hamityanik/ULP-Weather-Logger/Arduino-Example-Code/images/2.png

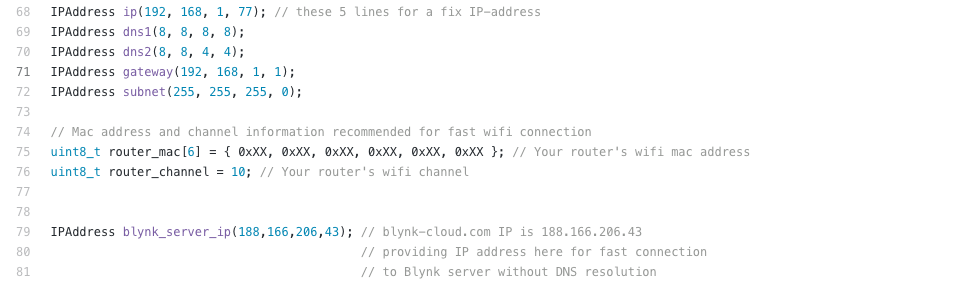
Arduino-Example-Code/images/2.png
