hamityanik/ULP-Weather-Logger/Images/@2.4v.png

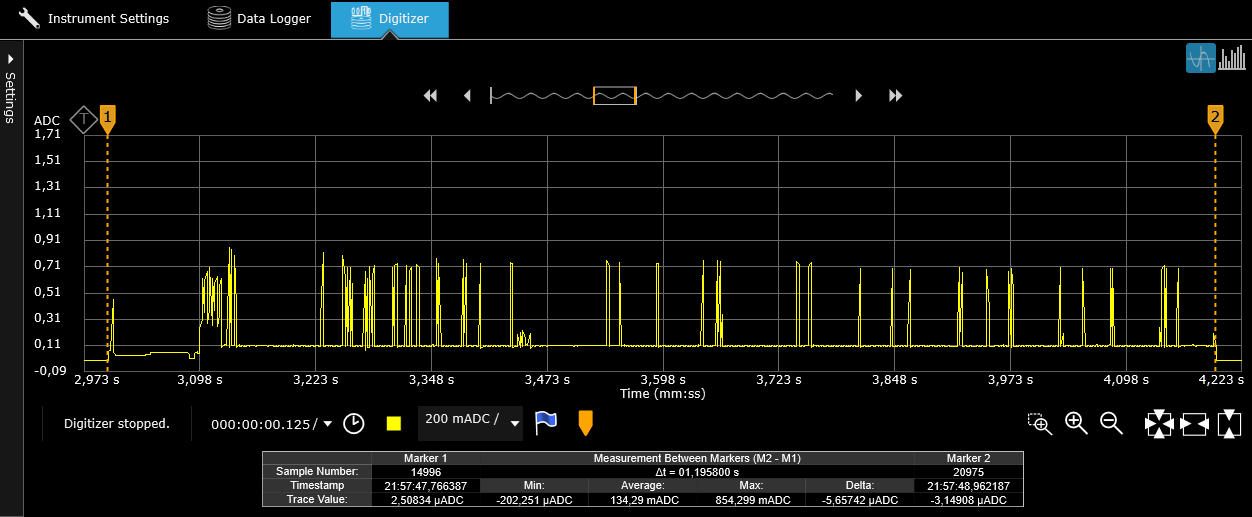
Images/@2.4v.png
