hamityanik/ULP-Weather-Logger/Images/@2v.png

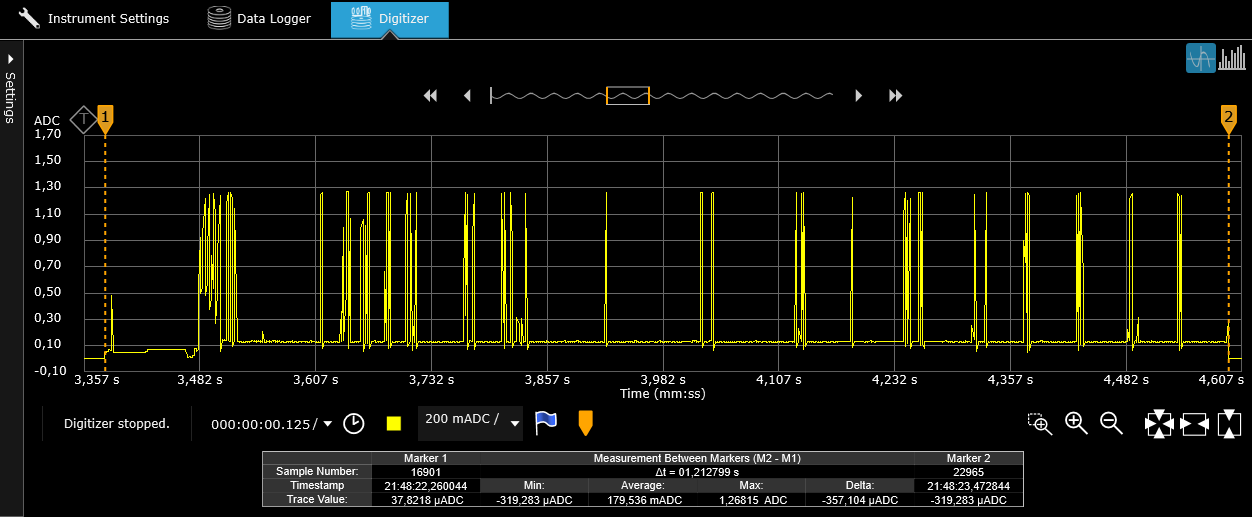
Images/@2v.png
