hamityanik/ULP-Weather-Logger/Images/_20170111_074019.JPG

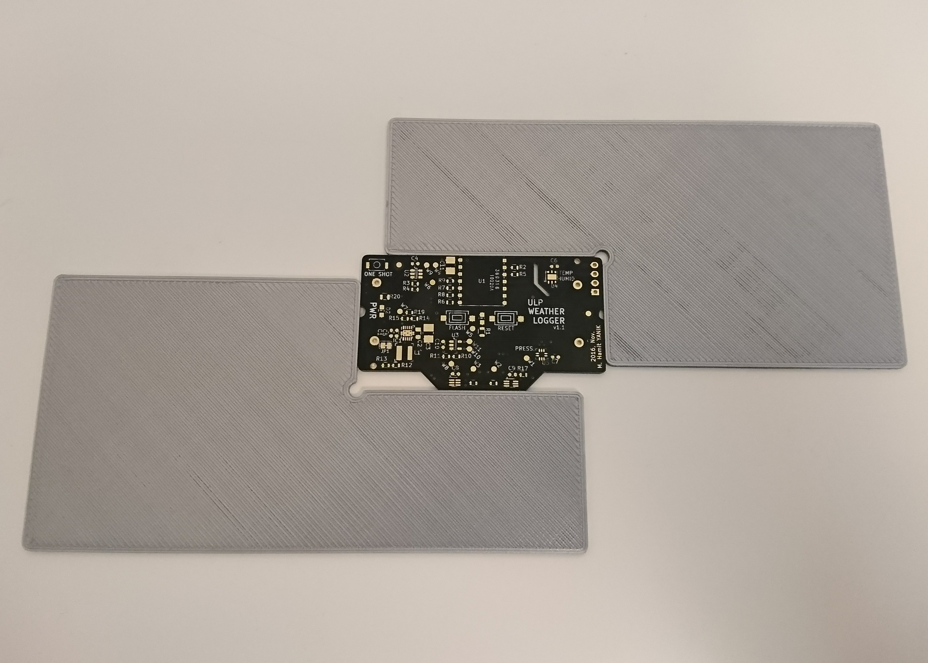
Images/_20170111_074019.JPG
