hamityanik/ULP-Weather-Logger/Images/DSC08371-v1.0.JPG

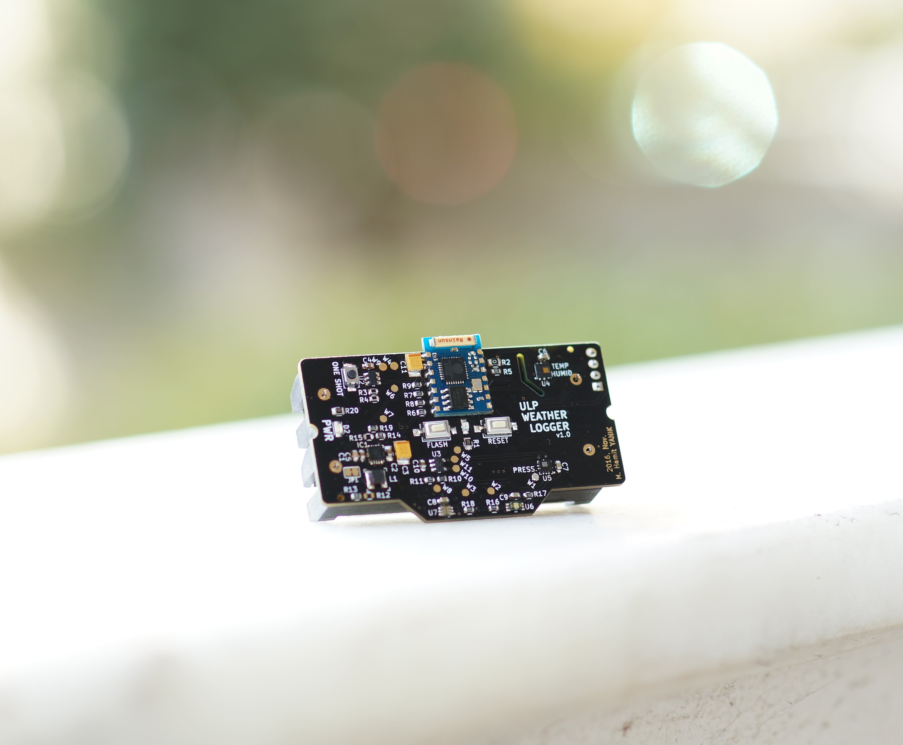
Images/DSC08371-v1.0.JPG
