hamityanik/ULP-Weather-Logger/Images/IMG_-4cxao2.jpg

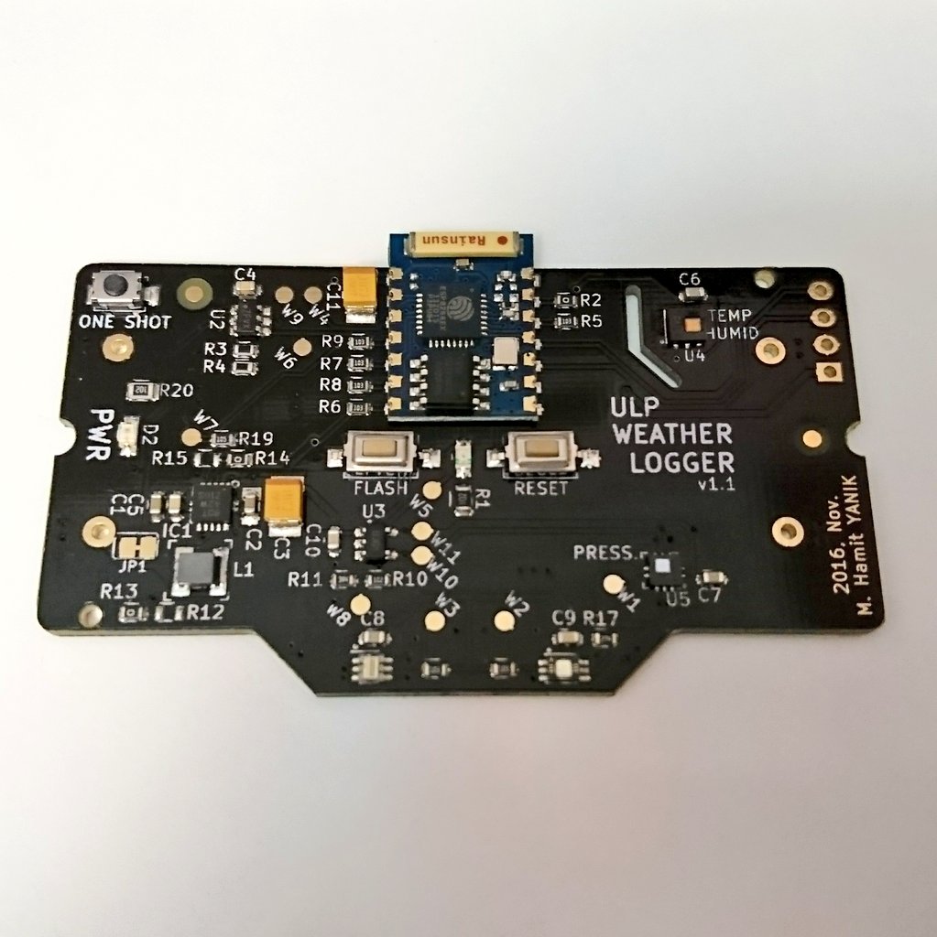
Images/IMG_-4cxao2.jpg
