hamityanik/ULP-Weather-Logger/Images/inSleep.png

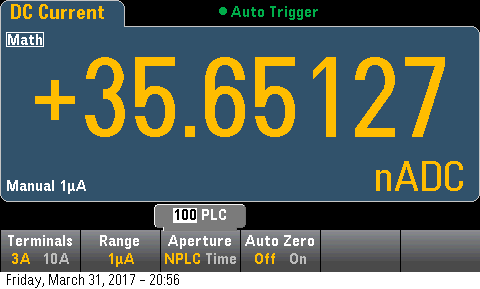
Images/inSleep.png
