hamityanik/ULP-Weather-Logger/Images/R3_R4_Selection_Table.png

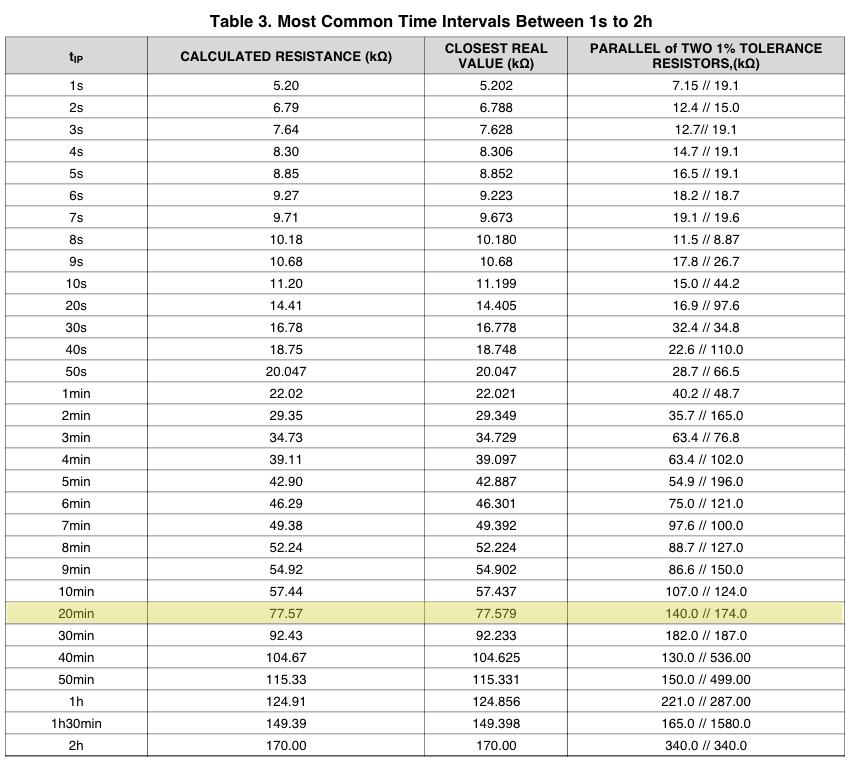
Images/R3_R4_Selection_Table.png
