hamityanik/ULP-Weather-Logger/Images/ULP-Weather-Logger-v1.1-KiCad-Render-Rear.png

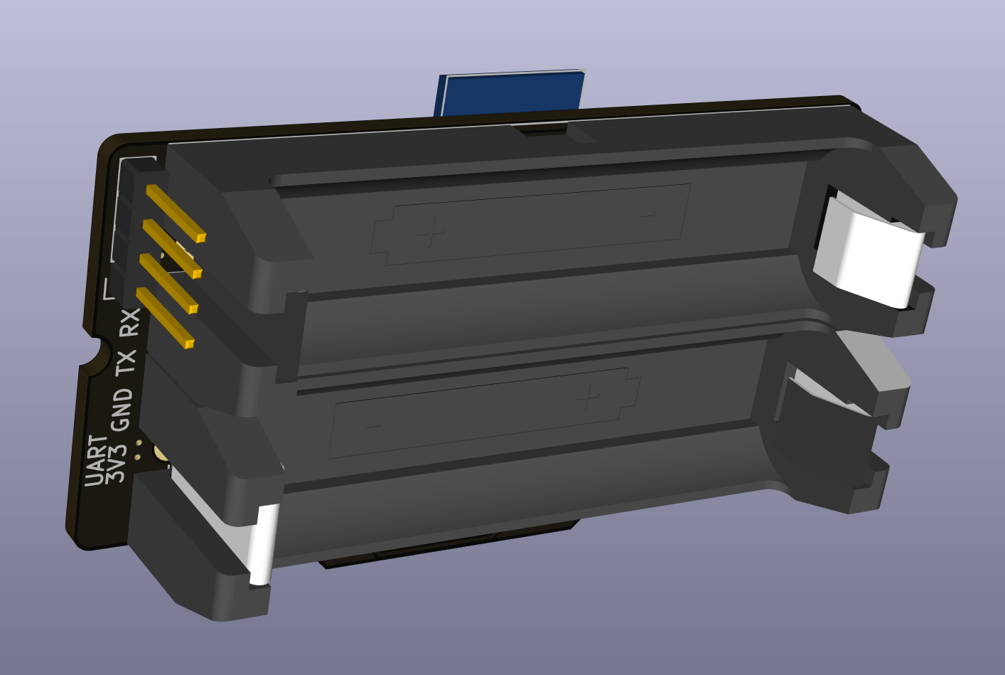
Images/ULP-Weather-Logger-v1.1-KiCad-Render-Rear.png
