hamityanik/ULP-Weather-Logger/Images/ULP-Weather-Logger-v1.1-KiCad-Render.png

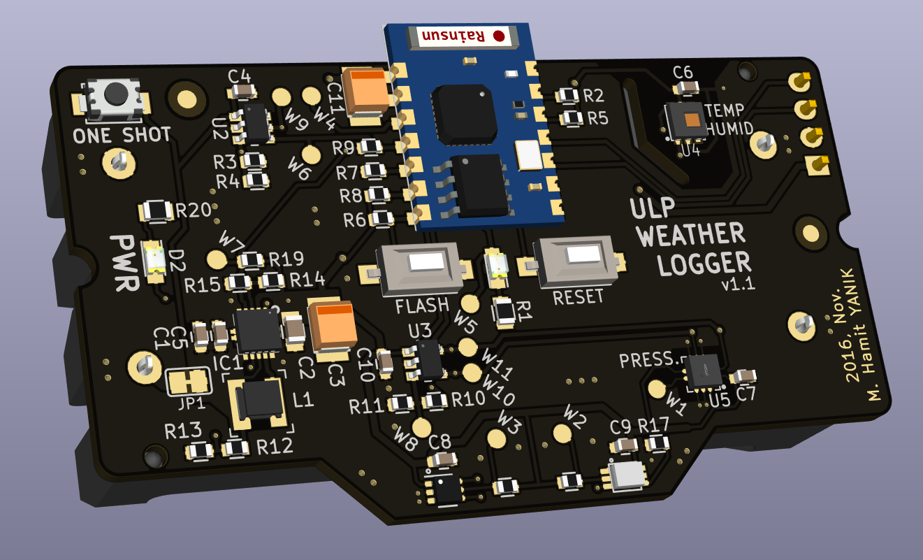
Images/ULP-Weather-Logger-v1.1-KiCad-Render.png
