hamityanik/ULP-Weather-Logger/Images/WL 2.jpg

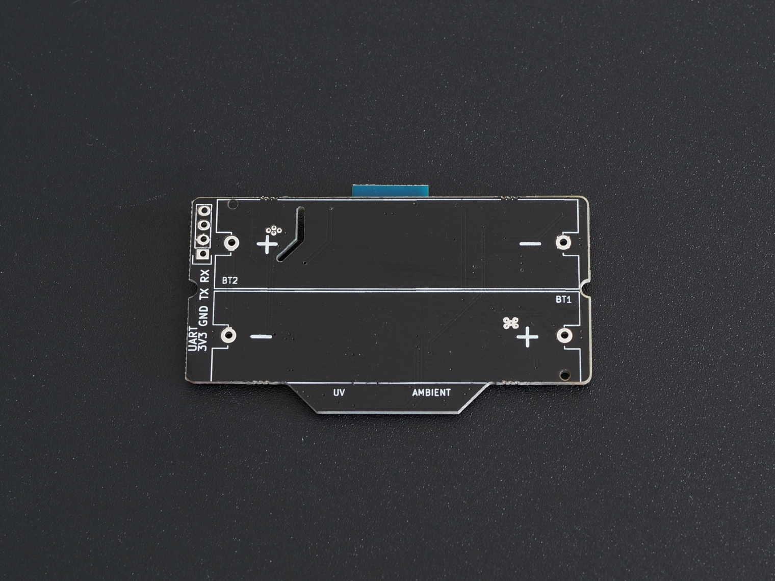
Images/WL 2.jpg
