hamityanik/ULP-Weather-Logger/Images/WL 3.jpg

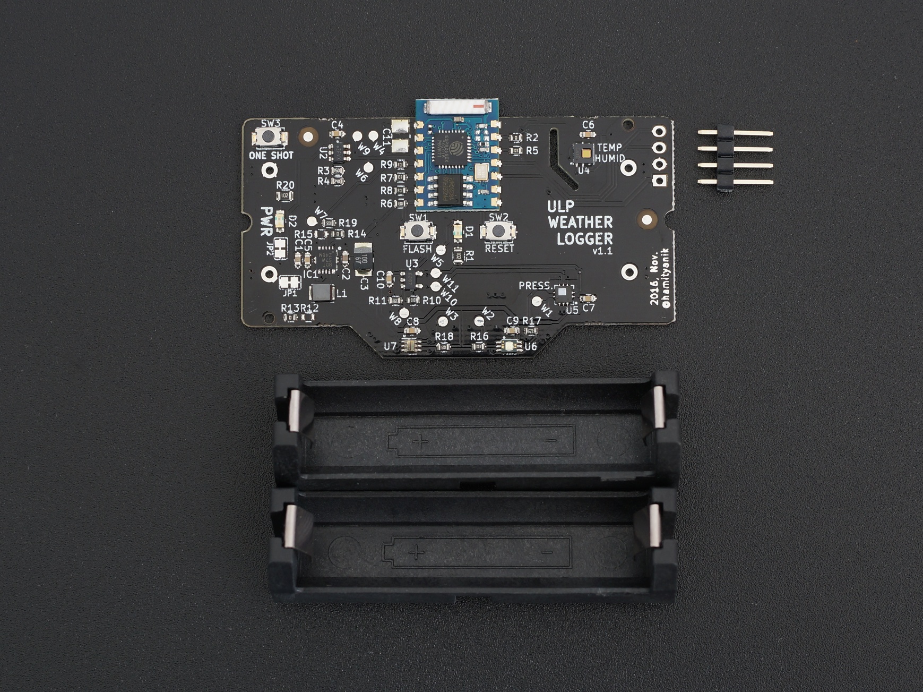
Images/WL 3.jpg
