hamityanik/ULP-Weather-Logger/Images/WL 4.jpg

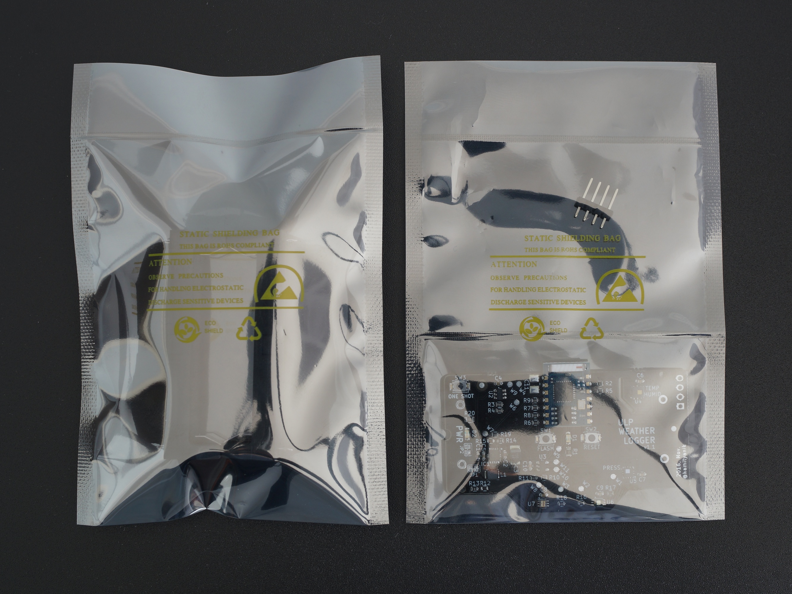
Images/WL 4.jpg
