hamityanik/ULP-Weather-Logger/Images/WL 5.jpg

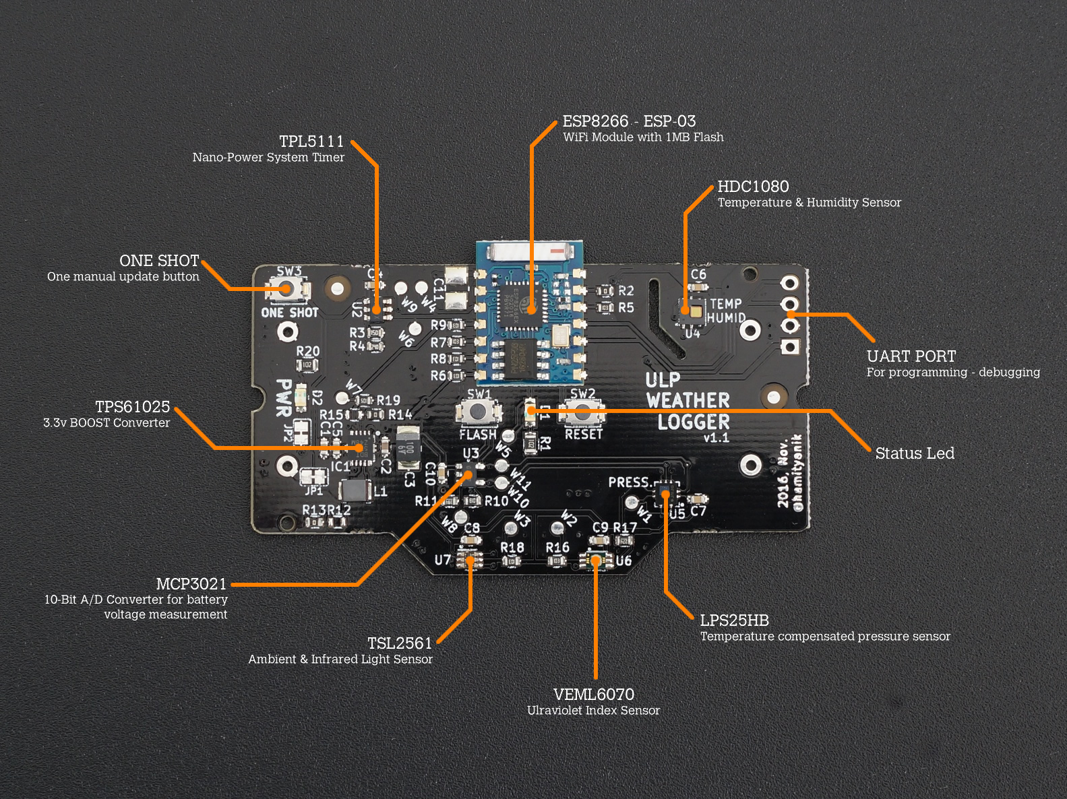
Images/WL 5.jpg
