hamityanik/ULP-Weather-Logger/Images/WL 6.jpg

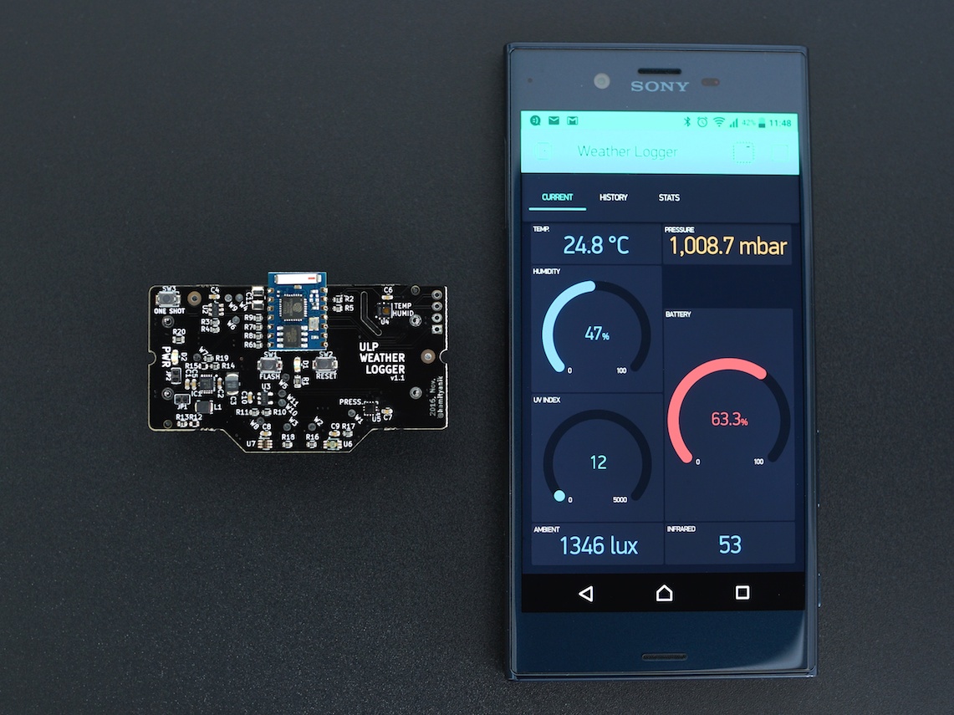
Images/WL 6.jpg
