hamityanik/ULP-Weather-Logger/Images/one_shot_manual_update.gif

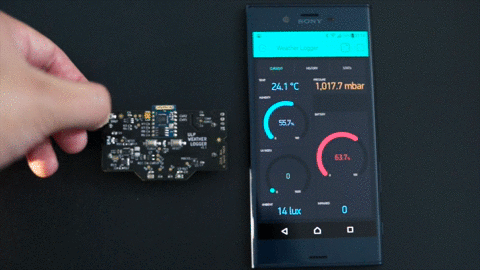
Images/one_shot_manual_update.gif
