hamityanik/ULP-Weather-Logger/KiCAD-design-files/images/esp-03-wiring.jpg

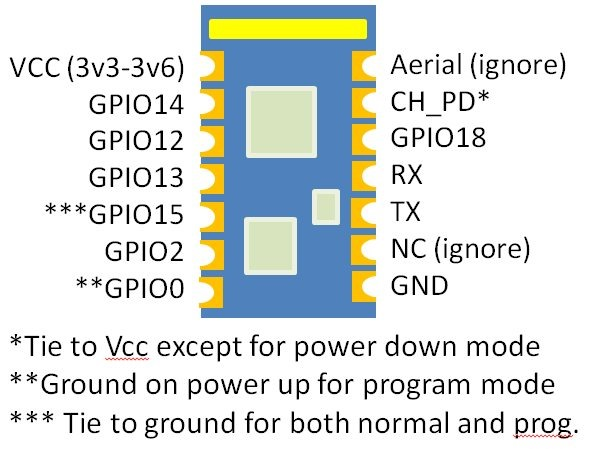
KiCAD-design-files/images/esp-03-wiring.jpg
